re-innovation/bwp/Projection_Unit_Software/firmware/DiagnosticMode.cpp

#include <Arduino.h>
#include "DiagnosticMode.h"
#include "ProjectorHeartbeat.h"
#include "SW1.h"
#include "DiagnosticFrameSyncMode.h"
#include "DiagnosticManualFeedMode.h"
#include "DiagnosticVolumeAdjustMode.h"
#include "DiagnosticNumberOfSamplesMode.h"
#include "DiagnosticStatUsesMode.h"
#include "DiagnosticStatSecondsMode.h"
#include "DiagnosticStatAvgSecondsMode.h"
#include "Mp3Player.h"
#include "Settings.h"

// Our global instance of the mode...
DiagnosticMode_ DiagnosticMode;

DiagnosticMode_::DiagnosticMode_()
{
}

void DiagnosticMode_::modeStart()
{
    DBLN(F("DiagnosticMode::modeStart()"));
    ProjectorHeartbeat.setMode(Heartbeat::Quick);
    Mp3Player.setVolume(Settings.volume());
    subMode = &DiagnosticManualFeedMode;
    subMode->start();
    _done = false;
}

void DiagnosticMode_::modeStop()
{
    DBLN(F("DiagnosticMode::modeStop()"));
    subMode->stop();
}

void DiagnosticMode_::modeUpdate()
{
    // Handle mode changes
    if (subMode->isFinished()) {
        if (subMode == &DiagnosticManualFeedMode) {
            switchSubMode(&DiagnosticFrameSyncMode);
        } else if (subMode == &DiagnosticFrameSyncMode) {
            switchSubMode(&DiagnosticVolumeAdjustMode);
        } else if (subMode == &DiagnosticVolumeAdjustMode) {
            switchSubMode(&DiagnosticNumberOfSamplesMode);
        } else if (subMode == &DiagnosticNumberOfSamplesMode) {
            switchSubMode(&DiagnosticStatUsesMode);
        } else if (subMode == &DiagnosticStatUsesMode) {
            switchSubMode(&DiagnosticStatSecondsMode);
        } else if (subMode == &DiagnosticStatSecondsMode) {
            switchSubMode(&DiagnosticStatAvgSecondsMode);
        } else if (subMode == &DiagnosticStatAvgSecondsMode) {
            _done = true;
        }
    }

    // Give timeslice to current sub-mode
    subMode->update();
}

bool DiagnosticMode_::isFinished()
{
    return _done;
}

void DiagnosticMode_::switchSubMode(Mode* mode)
{
    subMode->stop();
    subMode = mode;
    subMode->start();
}
