re-innovation/bwp/Projection_Unit_Software/firmware/NormalMode.cpp

#include <Arduino.h>
#include <MutilaDebug.h>
#include <EMAVDivSampler.h>
#include "NormalMode.h"
#include "ProjectorHeartbeat.h"
#include "SW1.h"
#include "Projector.h"
#include "Mp3Player.h"
#include "Settings.h"

EMAVDivSampler VoltageSampler(VIN_MONITOR_PIN, VIN_R1, VIN_R2, VIN_REF, VIN_PERIOD_MS, VIN_EMA_ALPHA);

// Our global mode object
NormalMode_ NormalMode(VoltageSampler, VIN_THRESH_LOW, VIN_THRESH_HIGH);

NormalMode_::NormalMode_(EMAVDivSampler& vSampler, const float vThreshLow, const float vThreshHigh) : 
    BrownoutMode(vSampler, vThreshLow, vThreshHigh)
{
}

void NormalMode_::modeStart()
{
    DBLN(F("NormalMode::modeStart"));
    Projector.setMute(false);
    Projector.setShutter(true);
    ProjectorHeartbeat.setMode(Heartbeat::Normal);
}

void NormalMode_::modeStop()
{
    DBLN(F("NormalMode::modeStop"));
    Mp3Player.stop();
    Settings.stop();
}

void NormalMode_::enterBrownout()
{
    // Typical use: save state to EEPROM etc...
    Serial.println(F("NormalMode::enterBrownout()"));
    ProjectorHeartbeat.setMode(Heartbeat::Slow);
    Projector.closeShutter();
    Projector.setStepperEnabled(false);
    Mp3Player.stop();
    Mp3Player.enable(false);
    Settings.stop();
    Settings.save();
}

void NormalMode_::exitBrownout()
{
    Serial.println(F("NormalMode::exitBrownout()"));
    ProjectorHeartbeat.setMode(Heartbeat::Normal);
    // Typical use: restore state from EEPROM
    Settings.run();
    Mp3Player.enable(true);
    Projector.setStepperEnabled(true);
}

void NormalMode_::modeUpdate()
{
    if (!brownedOut()) {
        Projector.update();
    }
}

bool NormalMode_::isFinished()
{
    return SW1.tapped() != 0 && !brownedOut();
}
