re-innovation/bwp/test8/Config.h

#pragma once

#define MP3_RX_PIN                  6
#define MP3_TX_PIN                  5
#define MP3_BUSY_PIN                10
#define MP3_VOLUME                  10
#define MP3_TRACK_ZERO              200
#define MP3_TRACK_POINT             210
#define MP3_TRACK_HOURS             211
#define MP3_TRACK_MINUTES           212
#define MP3_TRACK_SECONDS           213
#define MP3_TRACK_NUMBER_OF_USES    214
#define MP3_TRACK_AVERAGE_RUNTIME   215
#define MP3_TRACK_TOTAL_RUNTIME     216
